ppisljar/freeesp32_audioplayer/main_board/pcb_v11_r7.pdf

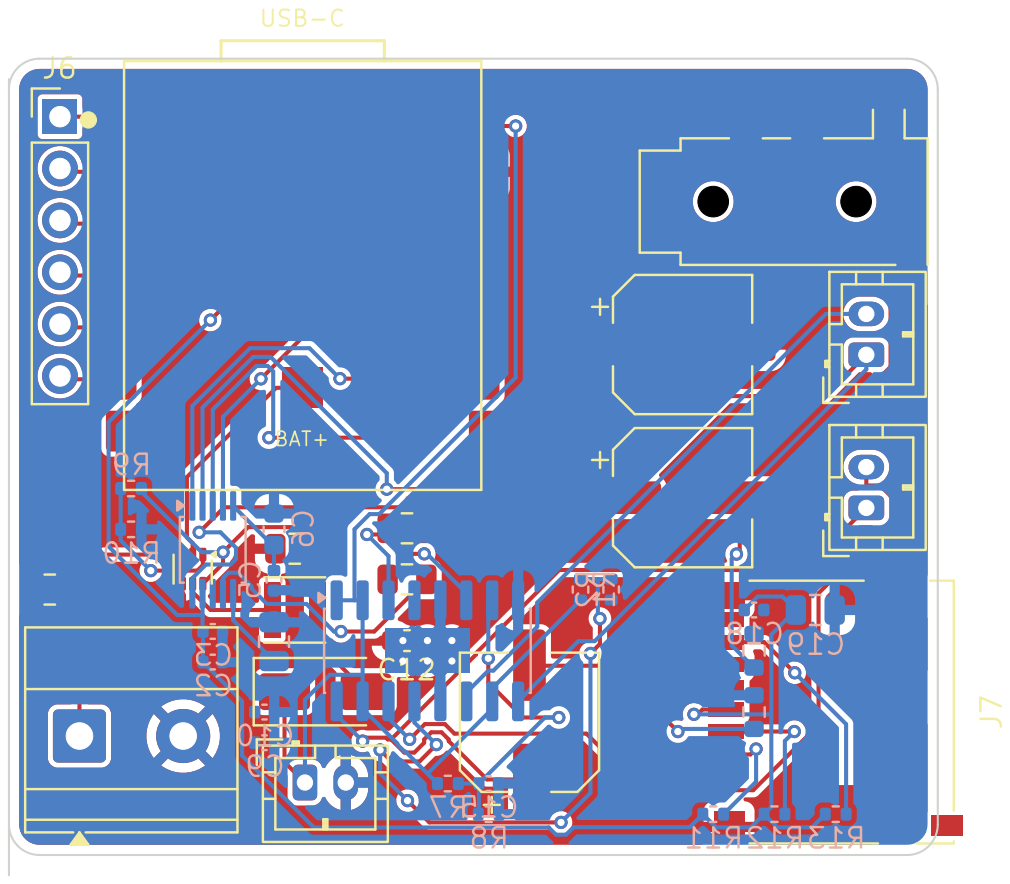
[picture p18: page 1]
