ppisljar/freeesp32_audioplayer/main_board/pcb_v11_r8.pdf

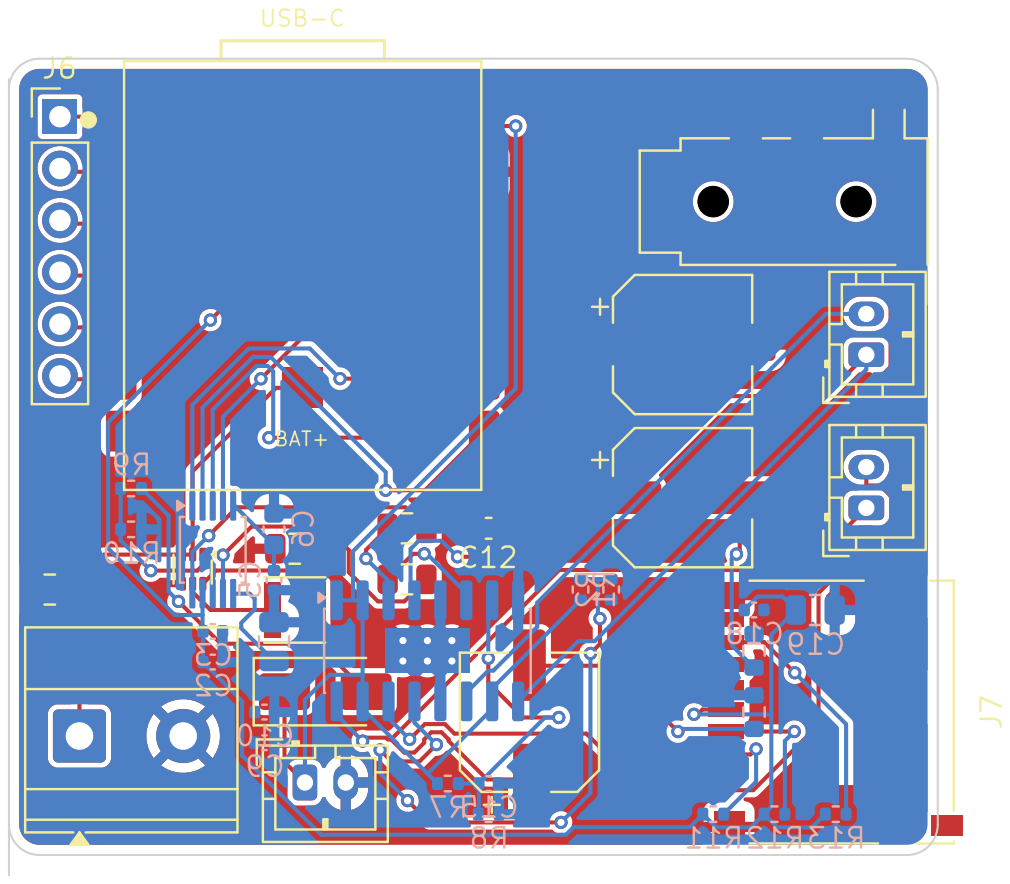
[picture p19: page 1]
