ppisljar/freeesp32_audioplayer/main_board/pcb_v11_r9.pdf

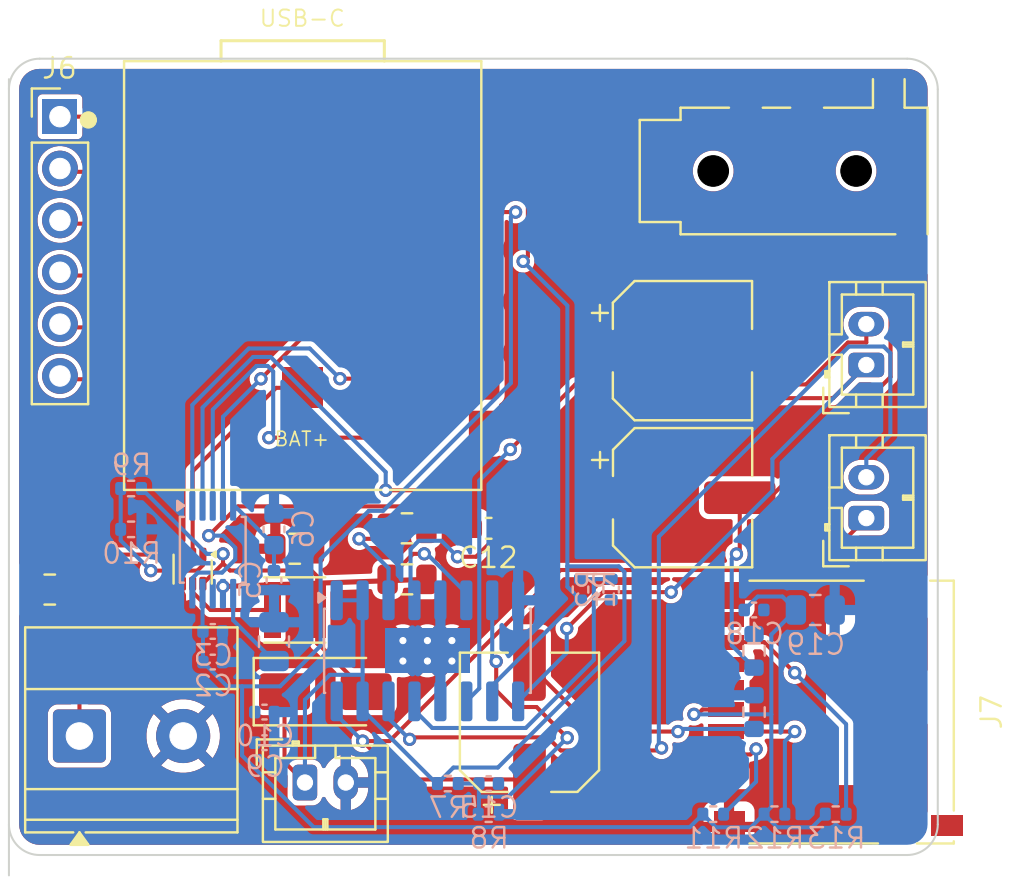
[picture p20: page 1]
