ppisljar/freeesp32_audioplayer/main_board/pcb_v11_rerouted.pdf

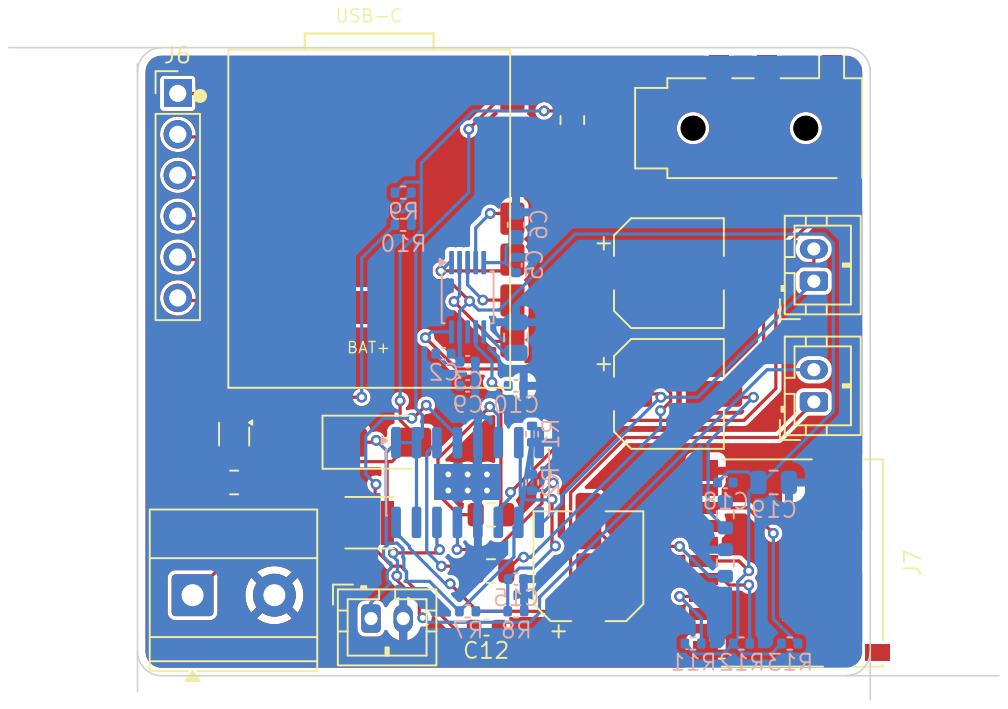
[picture p21: page 1]
