ppisljar/freeesp32_audioplayer/main_board/pcb_v2.pdf

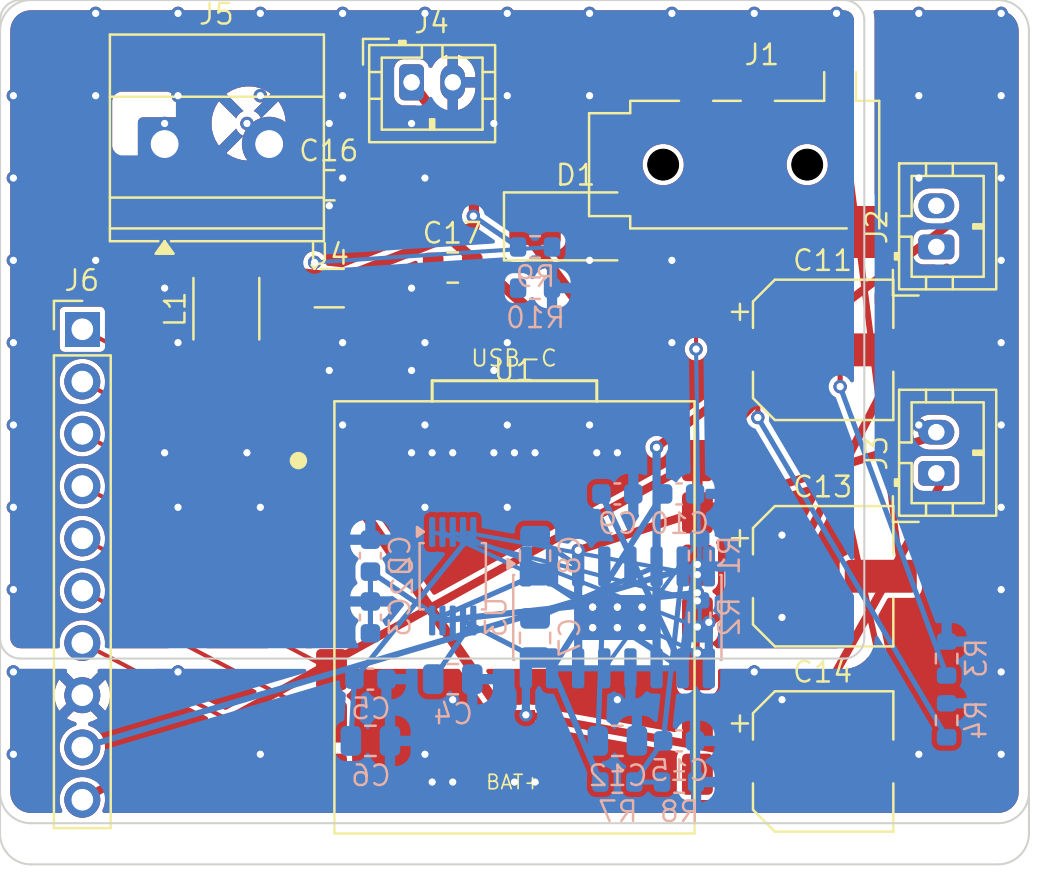
[picture p22: page 1]
